Asongnabrilan-nso/PlastiSense/assets/DRV5056 Hall effect sensor.jpg

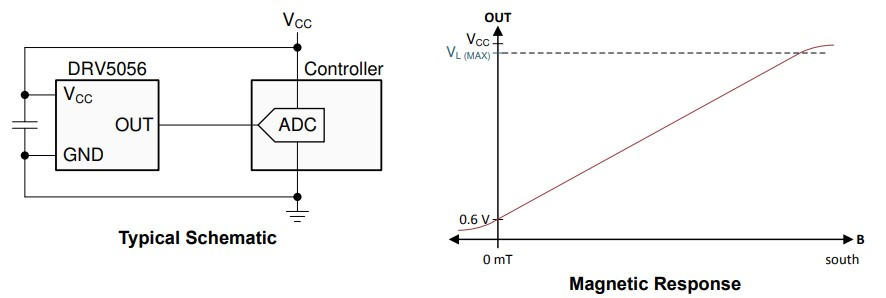
assets/DRV5056 Hall effect sensor.jpg
