Asongnabrilan-nso/PlastiSense/assets/DRV5056 Hall effect sensor_1.jpg

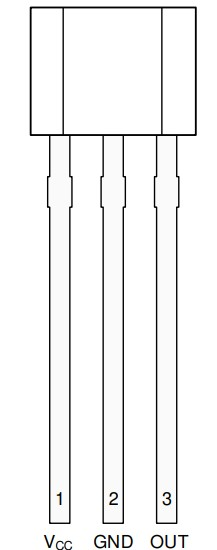
assets/DRV5056 Hall effect sensor_1.jpg
