Asongnabrilan-nso/PlastiSense/assets/Functional Block Diagram.jpg

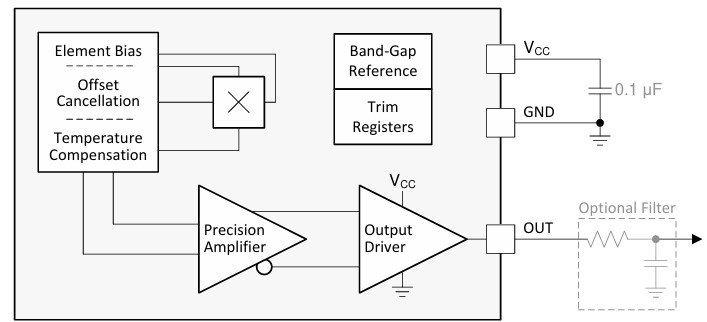
assets/Functional Block Diagram.jpg
