Asongnabrilan-nso/PlastiSense/assets/magnetic flux.jpg

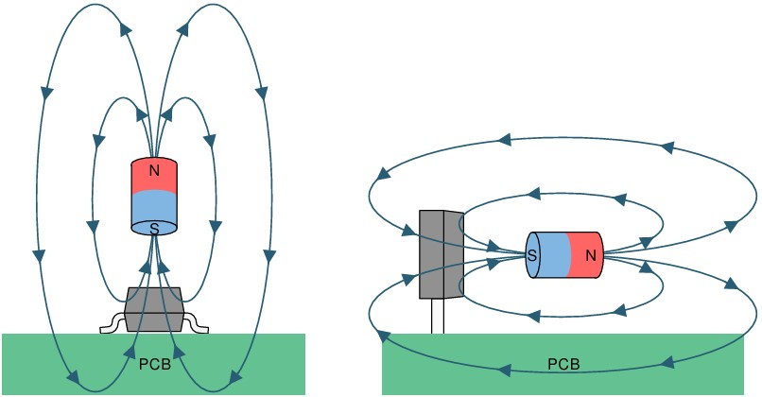
assets/magnetic flux.jpg
