Asongnabrilan-nso/PlastiSense/assets/PlastiSense v1.png

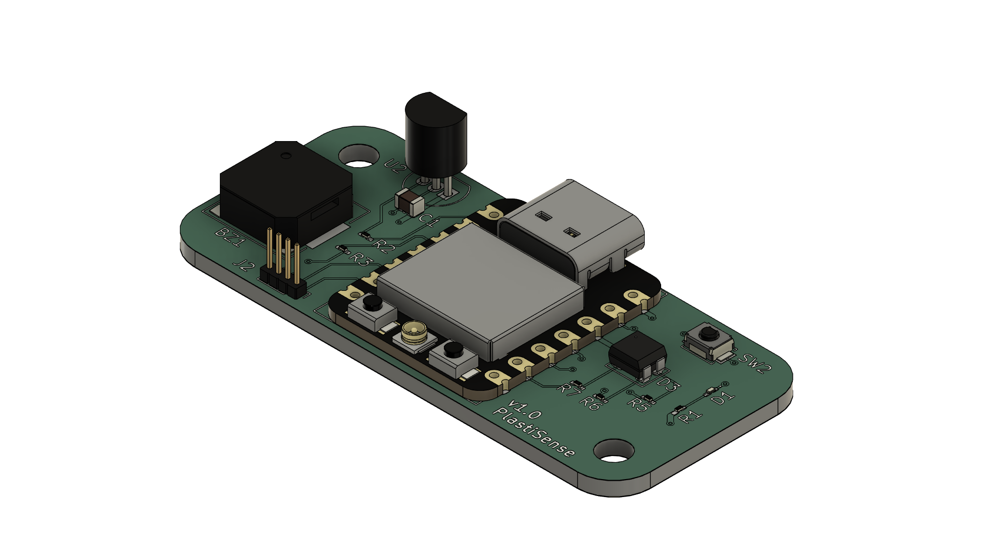
assets/PlastiSense v1.png
