Asongnabrilan-nso/PlastiSense/assets/PlastiSense v31.png

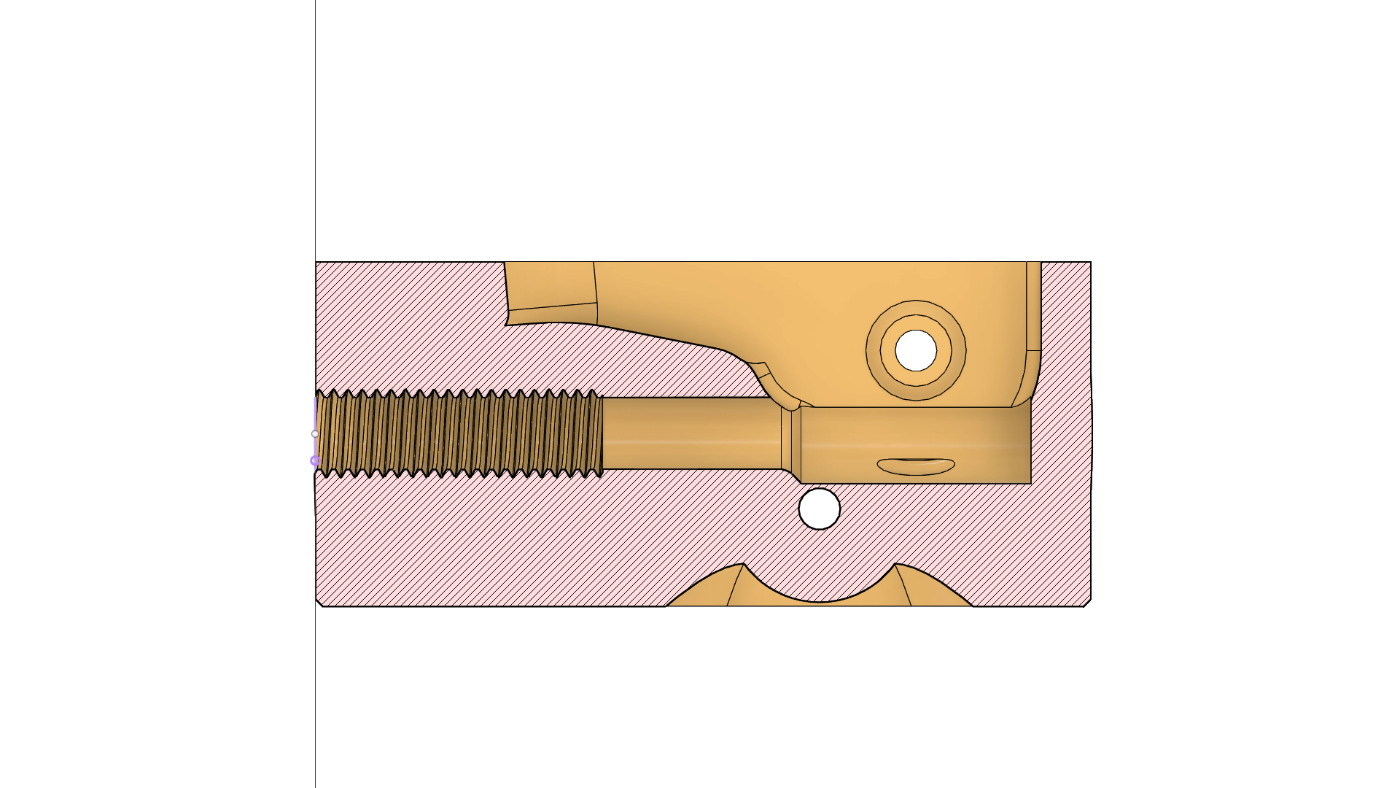
assets/PlastiSense v31.png
