Asongnabrilan-nso/PlastiSense/assets/PlastiSense-1 v15.png

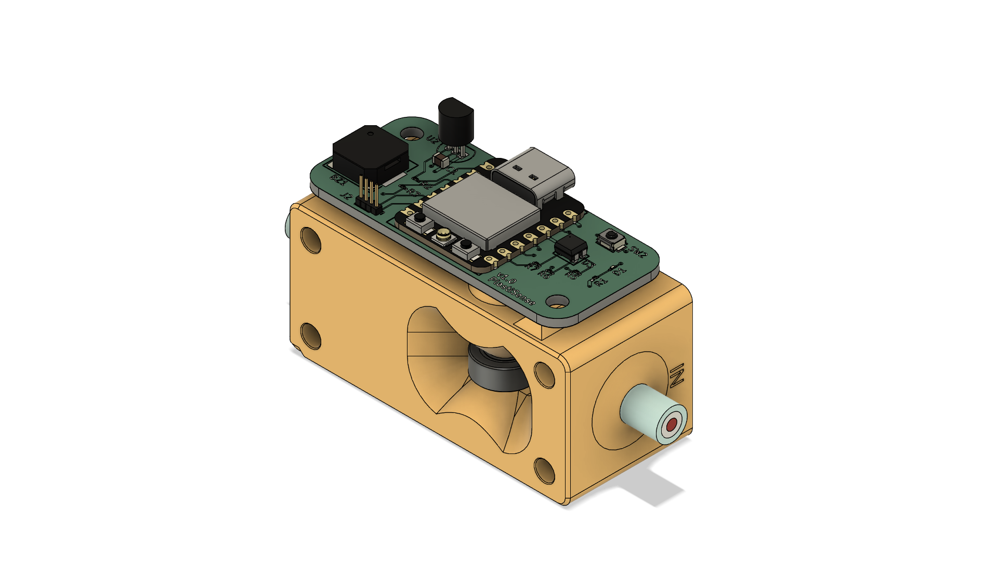
assets/PlastiSense-1 v15.png
