Asongnabrilan-nso/PlastiSense/assets/PlastiSense-2v1.png

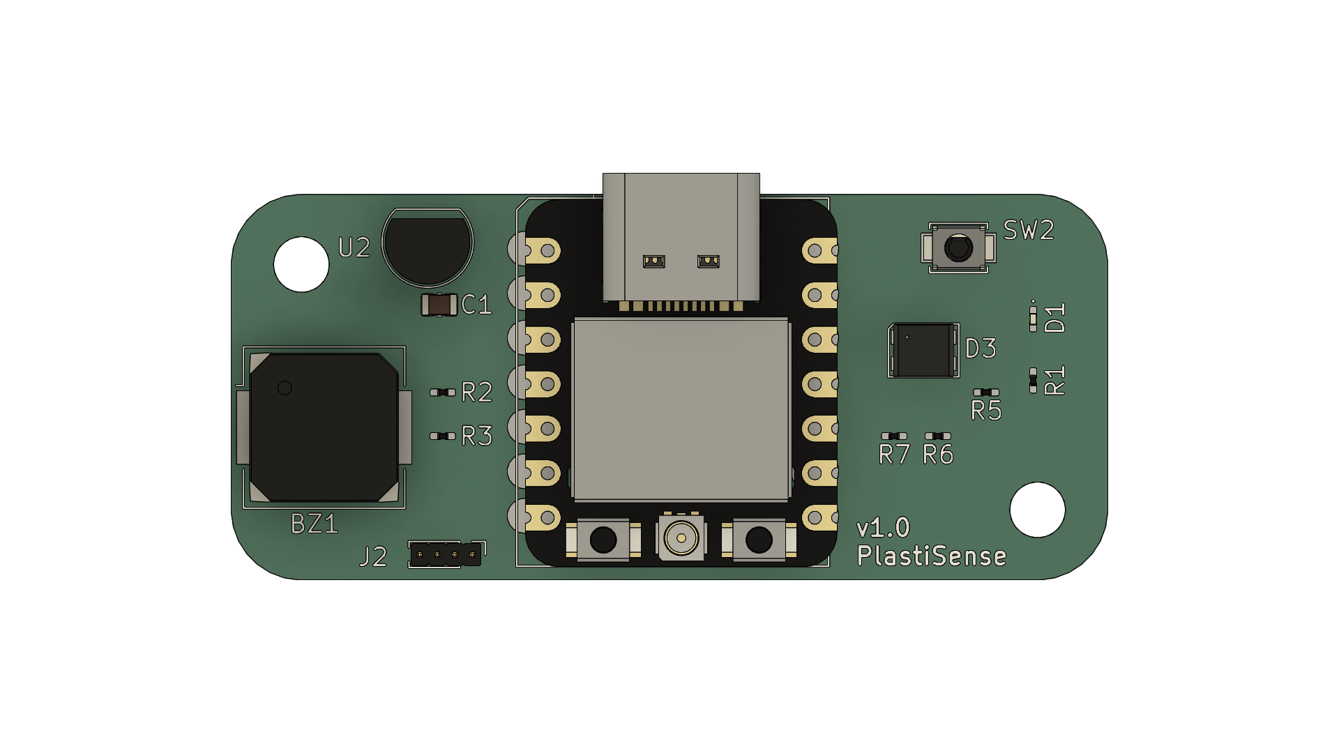
assets/PlastiSense-2v1.png
