Asongnabrilan-nso/PlastiSense/assets/PlastiSense-3 v15.png

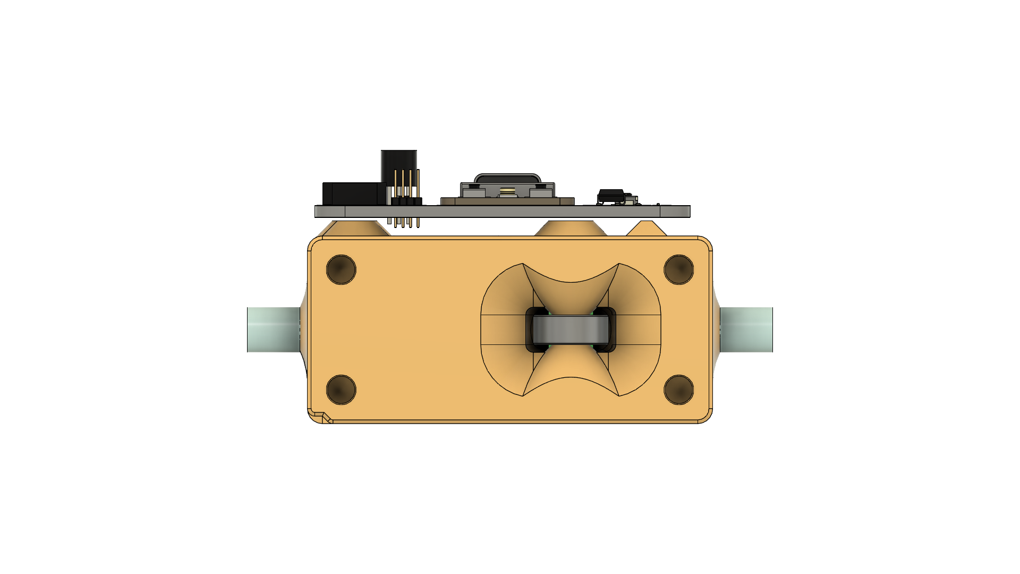
assets/PlastiSense-3 v15.png
