Asongnabrilan-nso/PlastiSense/assets/PlastiSense-4 v15.png

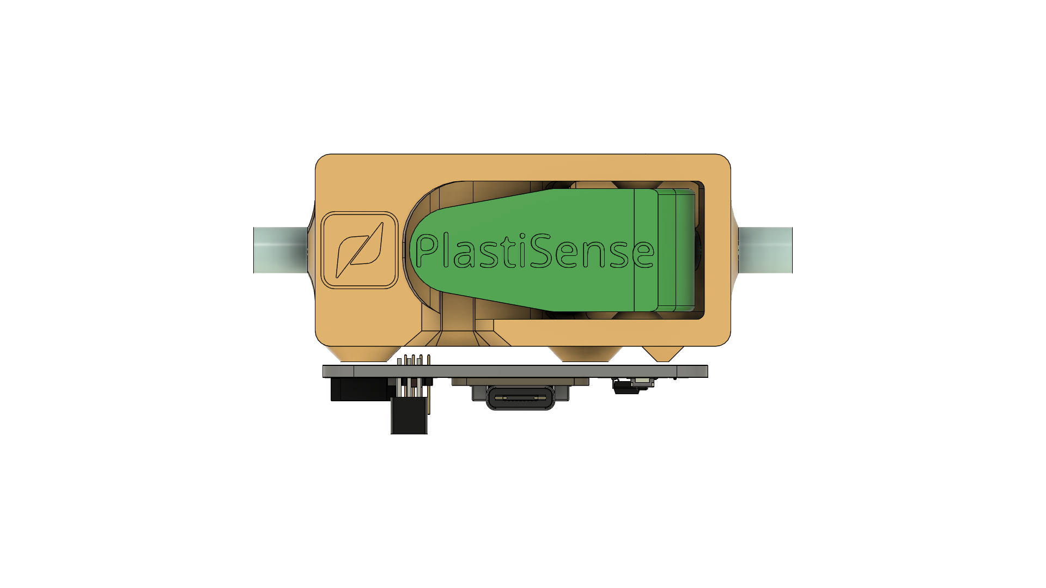
assets/PlastiSense-4 v15.png
