Asongnabrilan-nso/PlastiSense/assets/PlastiSense-5v15.png

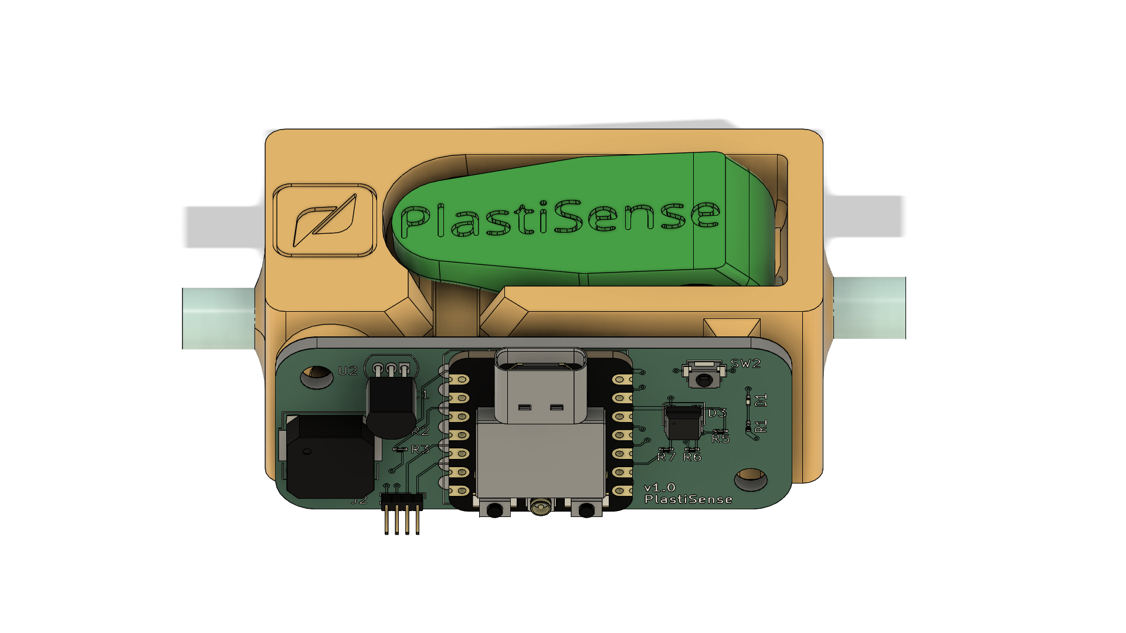
assets/PlastiSense-5v15.png
