Asongnabrilan-nso/PlastiSense/assets/PlastiSense-7.png

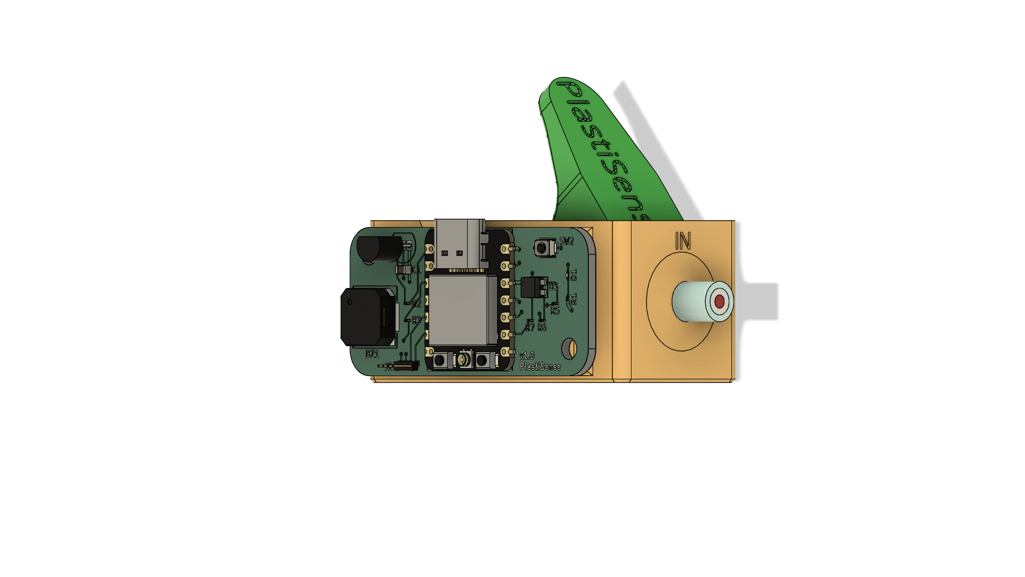
assets/PlastiSense-7.png
