Asongnabrilan-nso/PlastiSense/assets/PlastiSense-8.png

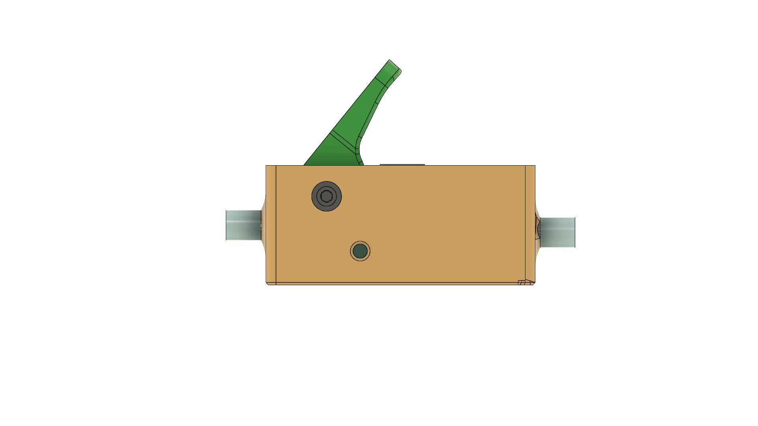
assets/PlastiSense-8.png
