Asongnabrilan-nso/PlastiSense/assets/PlastiSense-9.png

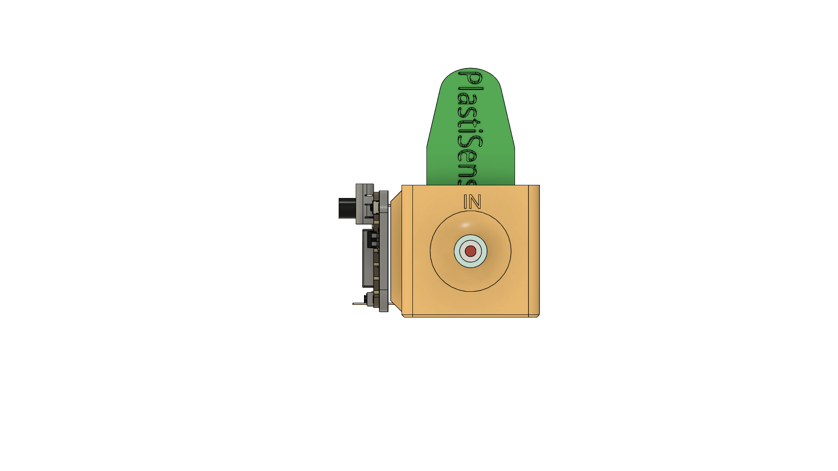
assets/PlastiSense-9.png
