Asongnabrilan-nso/PlastiSense/assets/PlastiSense-10.png

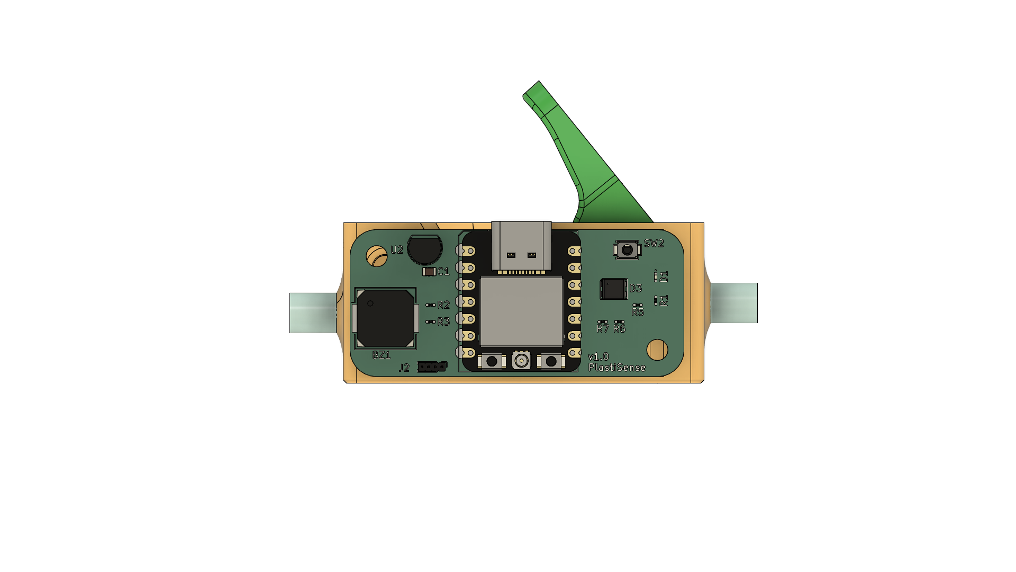
assets/PlastiSense-10.png
