Asongnabrilan-nso/PlastiSense/assets/PlastiSense-11.png

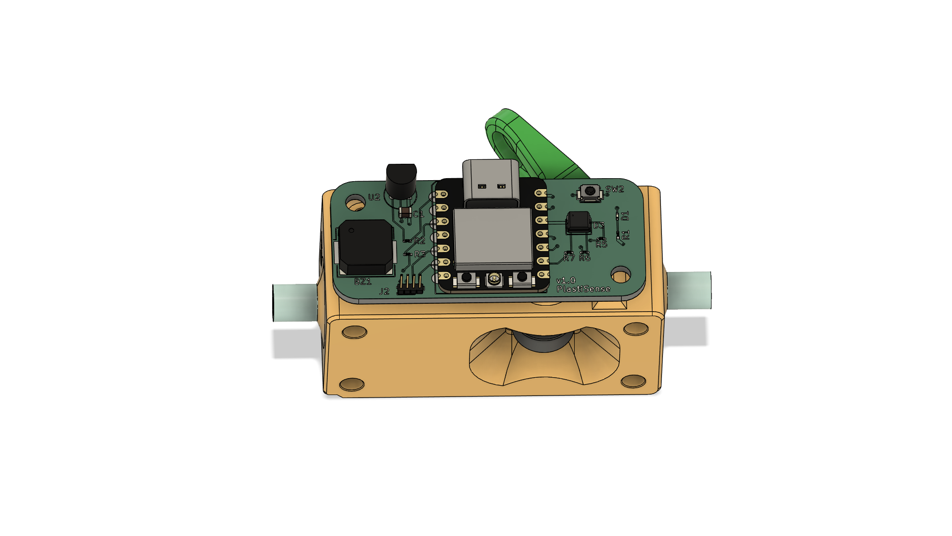
assets/PlastiSense-11.png
