Asongnabrilan-nso/PlastiSense/assets/PlastiSense-12.png

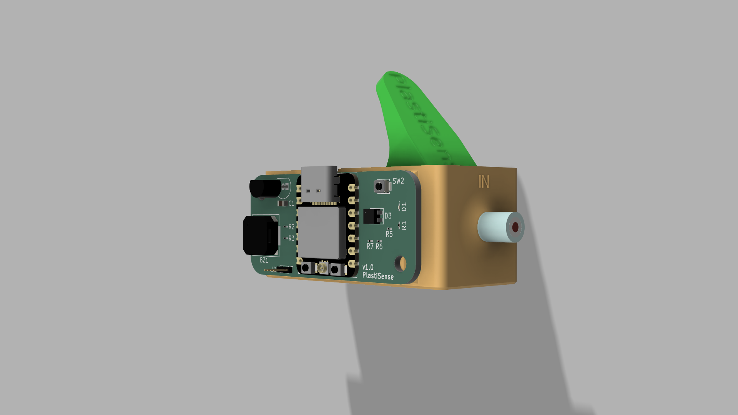
assets/PlastiSense-12.png
