Asongnabrilan-nso/PlastiSense/assets/PlastiSense-13.png

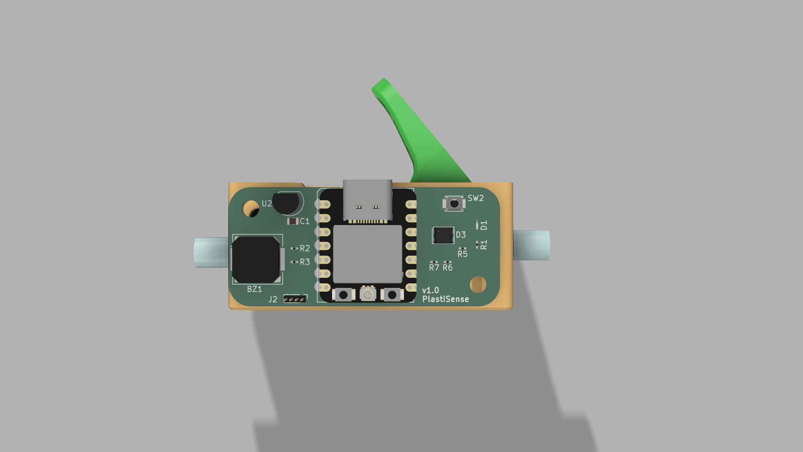
assets/PlastiSense-13.png
