Asongnabrilan-nso/PlastiSense/assets/PlastiSense-14.png

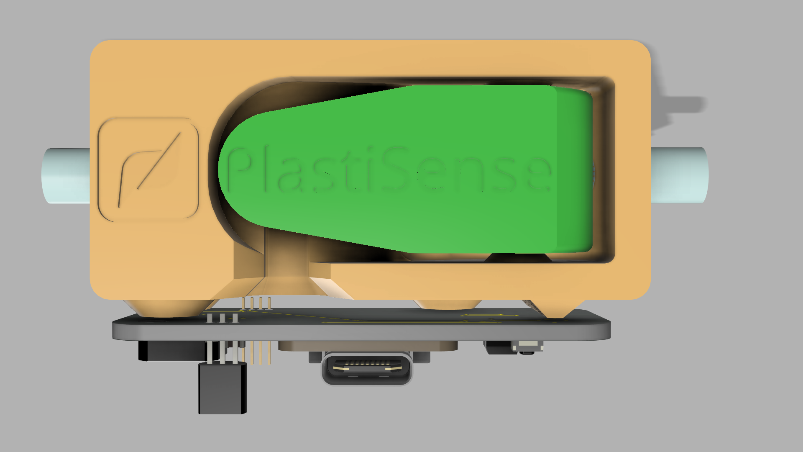
assets/PlastiSense-14.png
