Asongnabrilan-nso/PlastiSense/assets/PlastiSense-15.png

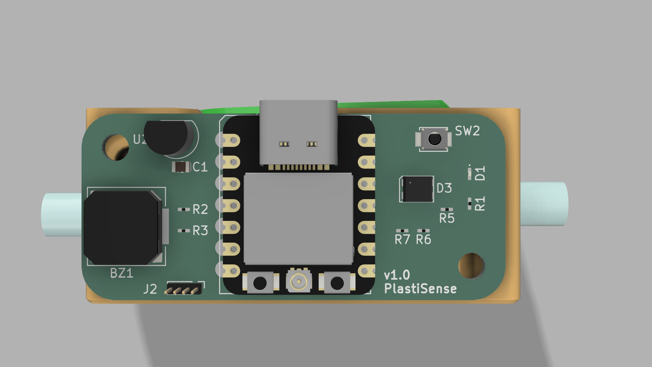
assets/PlastiSense-15.png
