Asongnabrilan-nso/PlastiSense/assets/PlastiSense-multiple-view.png

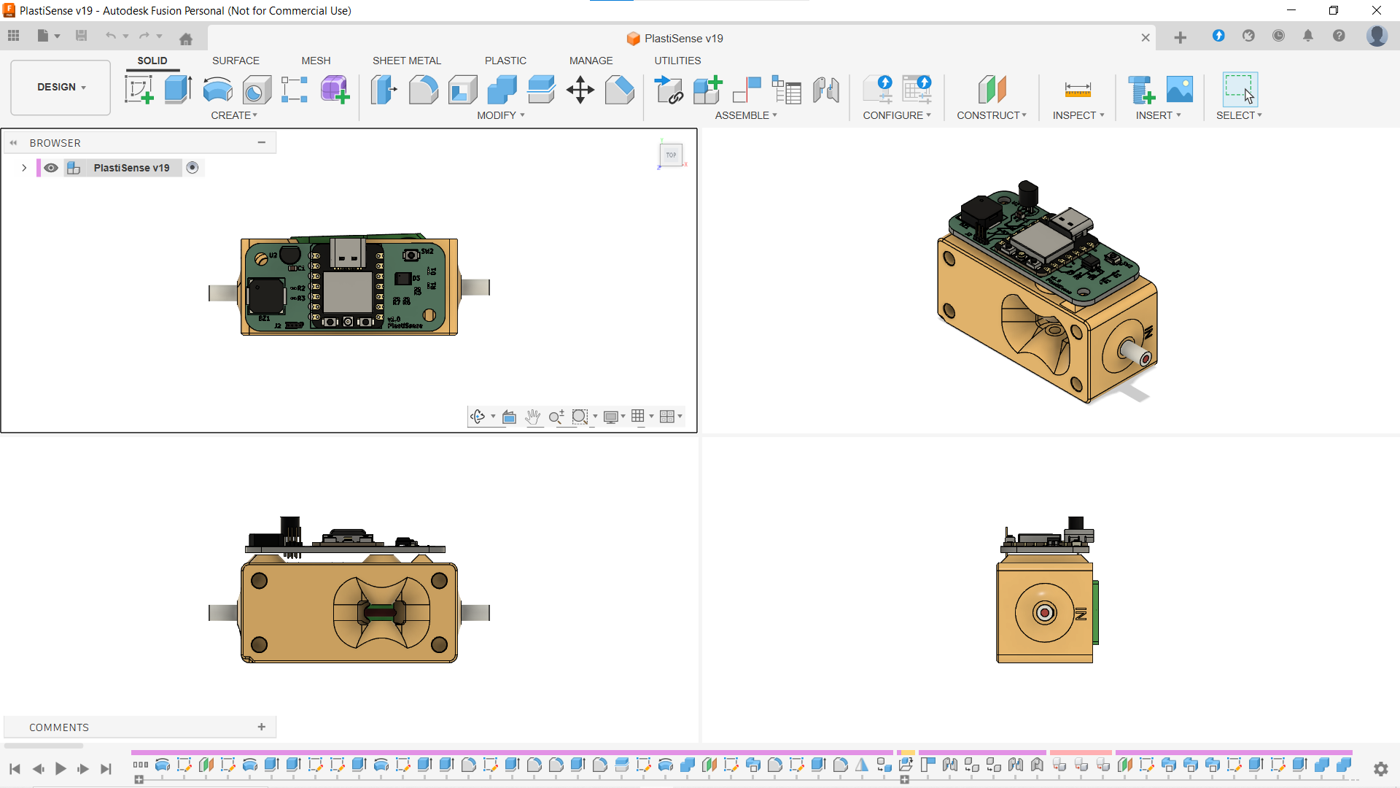
assets/PlastiSense-multiple-view.png
