Asongnabrilan-nso/PlastiSense/assets/python scripts.jpg

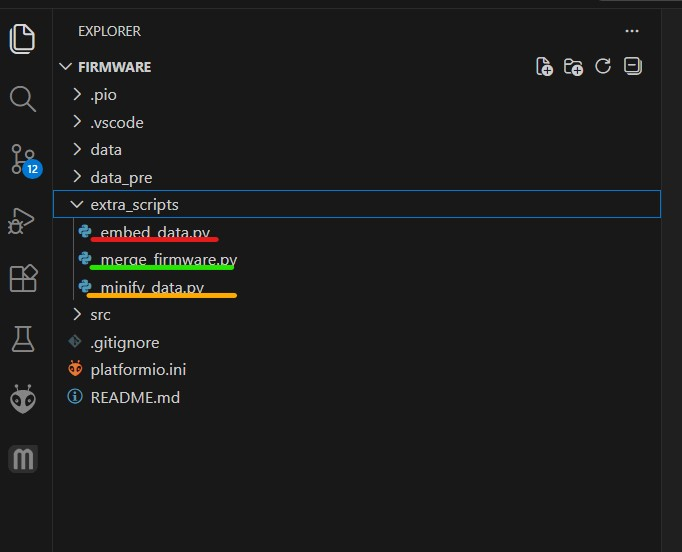
assets/python scripts.jpg
