Asongnabrilan-nso/PlastiSense/assets/Serial API.jpg

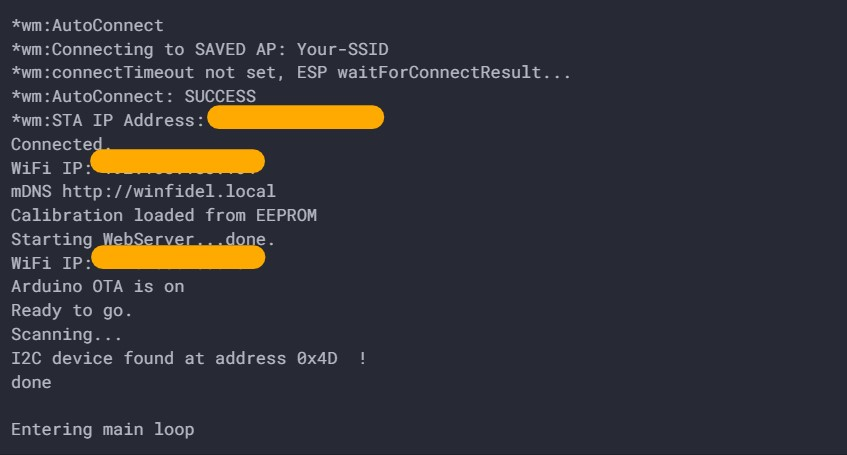
assets/Serial API.jpg
