Asongnabrilan-nso/PlastiSense/assets/Web1.png

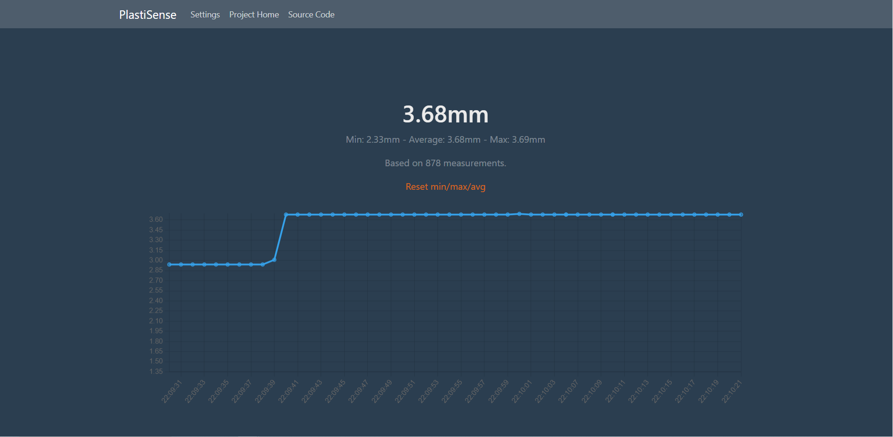
assets/Web1.png
