Asongnabrilan-nso/PlastiSense/assets/web2.png

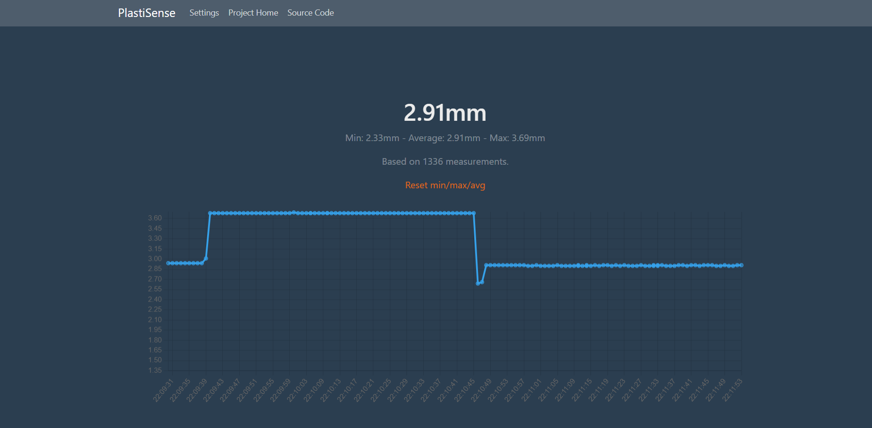
assets/web2.png
