Asongnabrilan-nso/PlastiSense/assets/web3.png

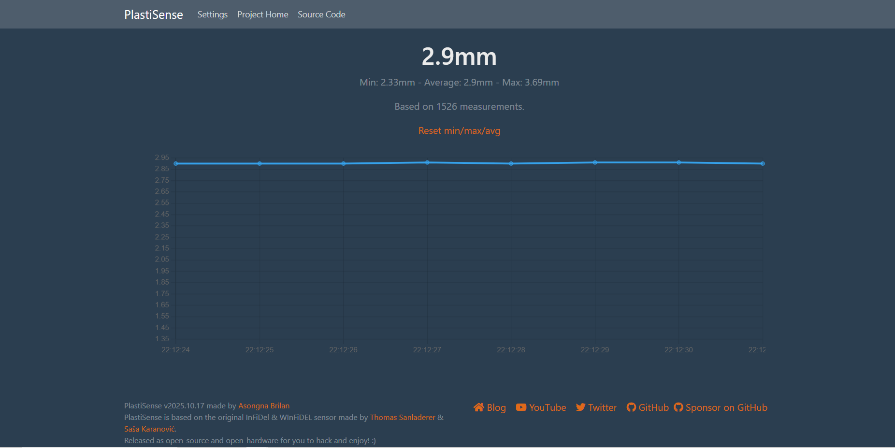
assets/web3.png
