Asongnabrilan-nso/PlastiSense/assets/web4.png

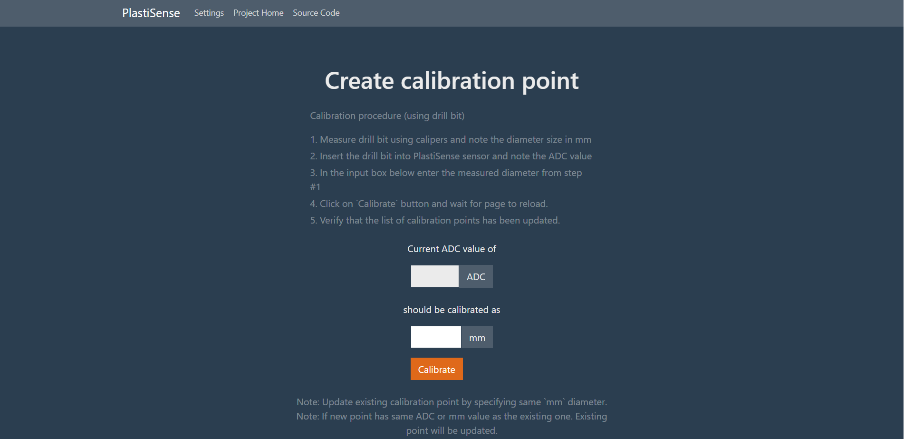
assets/web4.png
