Asongnabrilan-nso/PlastiSense/assets/web5.png

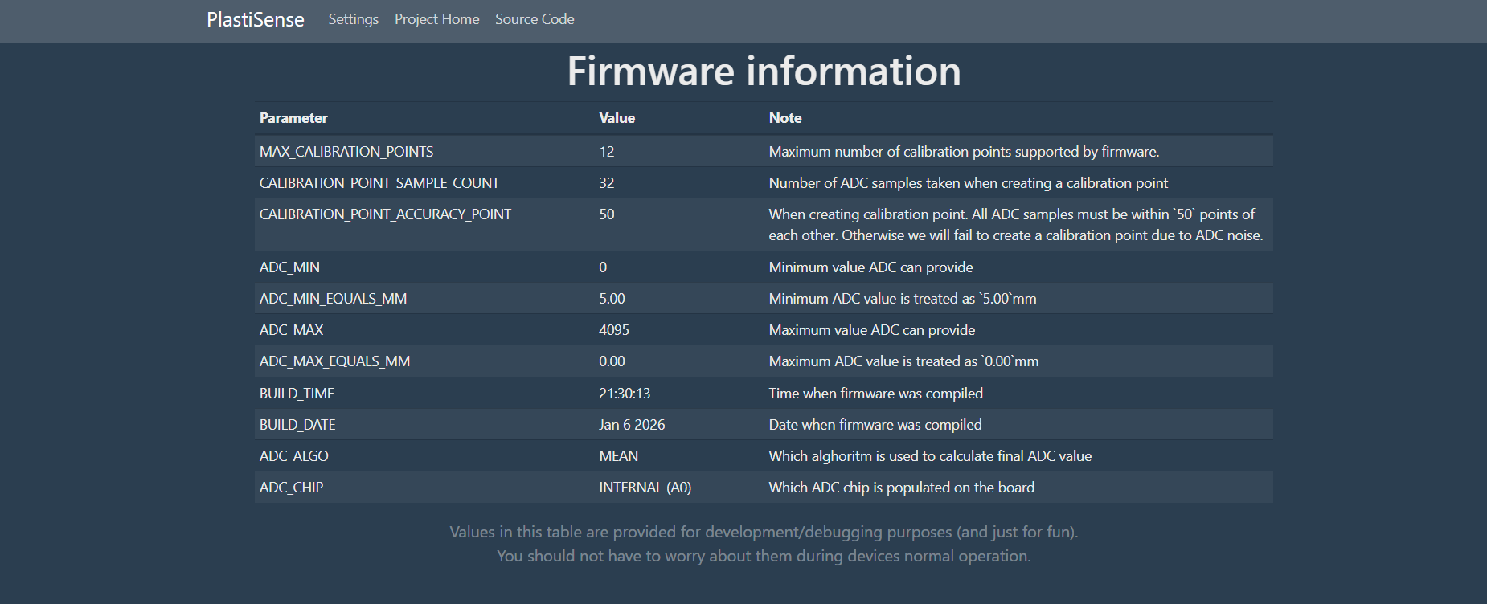
assets/web5.png
