Asongnabrilan-nso/PlastiSense/assets/WiFi-setup.png

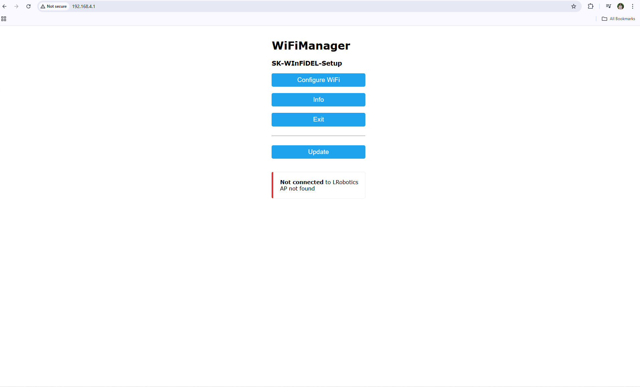
assets/WiFi-setup.png
